josbouten/Ratchet-O-Matic/src/Debug.hpp

#ifndef __DEBUG_H
    #define __DEBUG_H

    #ifdef DEBUG
        #include "LibPrintf.h" 
        #define debug_begin(z) Serial.begin(z)
        #define debug_print(z) printf(z)
        #define debug_print2(z, y) printf(z, y)
        #define debug_print3(z, y, x) printf(z, y, x)
        #define debug_print4(z, y, x, w) printf(z, y, x, w)
        #define debug_print5(z, y, x, w, v) printf(z, y, x, w, v)
        #define debug_print6(z, y, x, w, v, u) printf(z, y, x, w, v, u)
        #define debug_print7(z, y, x, w, v, u, t) printf(z, y, x, w, v, u, t)
        #define debug_print8(z, y, x, w, v, u, t, s) printf(z, y, x, w, v, u, t, s)
        #define debug_delay(z) delay(z)
    #else
        #define debug_begin(x)
        #define debug_print(x)
        #define debug_print2(z, y)
        #define debug_print3(z, y, x)
        #define debug_print4(z, u, x, w)
        #define debug_print5(z, y, x, w, v)
        #define debug_print6(z, y, x, w, v, u)
        #define debug_print7(z, y, x, w, v, u, t)
        #define debug_print8(z, y, x, w, v, u, t, s)
        #define debug_delay(z)
    #endif

#endif
